washishi/nekomimi_led/docs/images/cable_connect.png

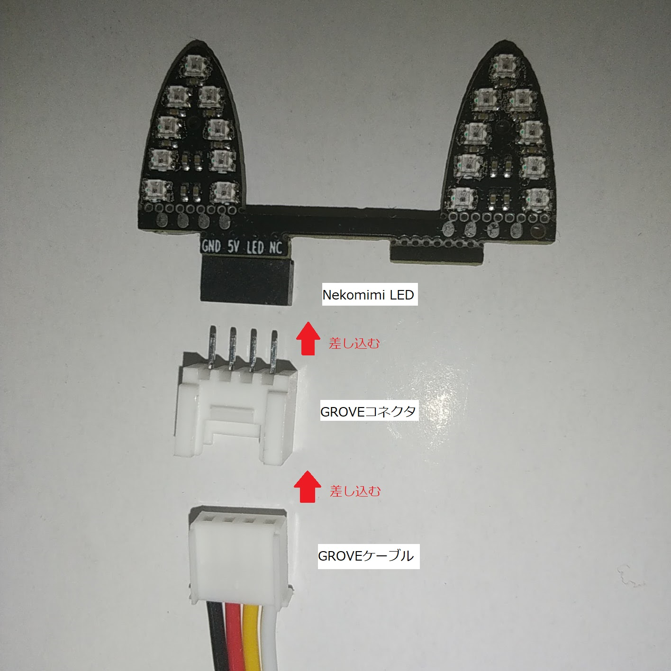
docs/images/cable_connect.png
